Aces-Electronics/ae-p703-screens/Front/FrontIO_Screen_Software/gui_project/ae/cache/thumb_362581445pirate_camp_co_290.png

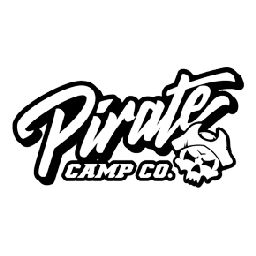
Front/FrontIO_Screen_Software/gui_project/ae/cache/thumb_362581445pirate_camp_co_290.png
