Aces-Electronics/ae-p703-screens/Rear/RearIO_MPPT/lifepo4_settings.webp

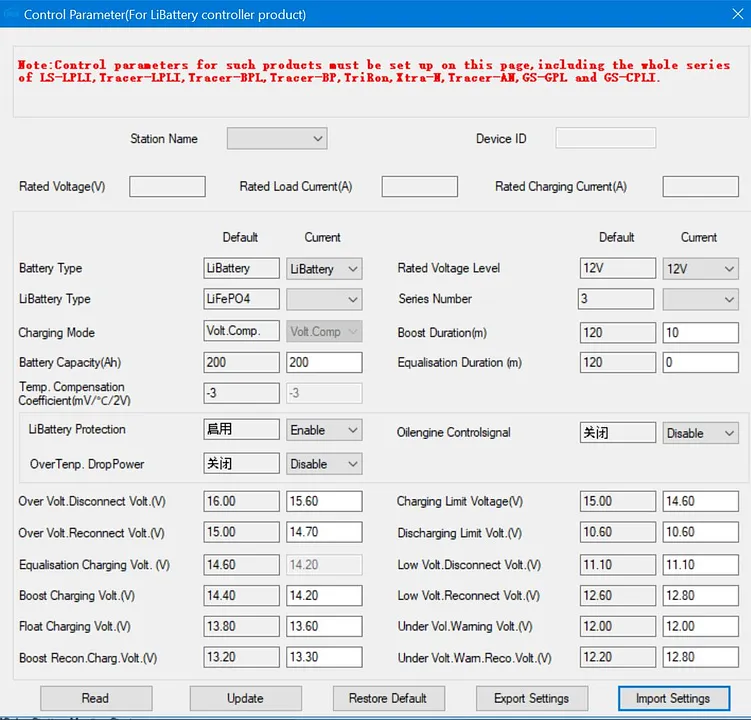
Rear/RearIO_MPPT/lifepo4_settings.webp
