Aces-Electronics/ae-p703-screens/Rear/RearIO_Screen_and_Battery_Cradle/DXF/folding/cradle_rear.dxf.png

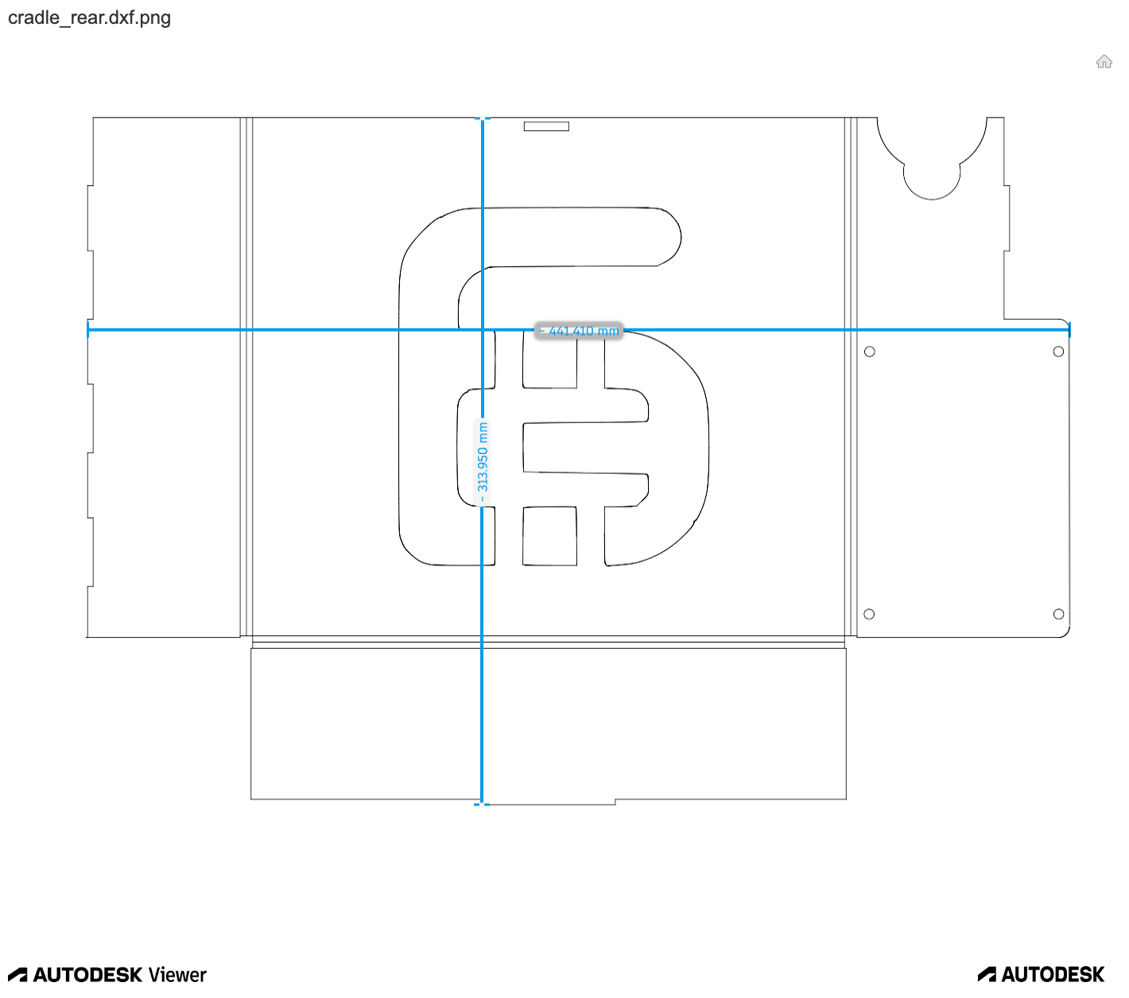
Rear/RearIO_Screen_and_Battery_Cradle/DXF/folding/cradle_rear.dxf.png
