Aces-Electronics/ae-p703-screens/Rear/RearIO_Screen_and_Battery_Cradle/DXF/folding/panel.dxf.png

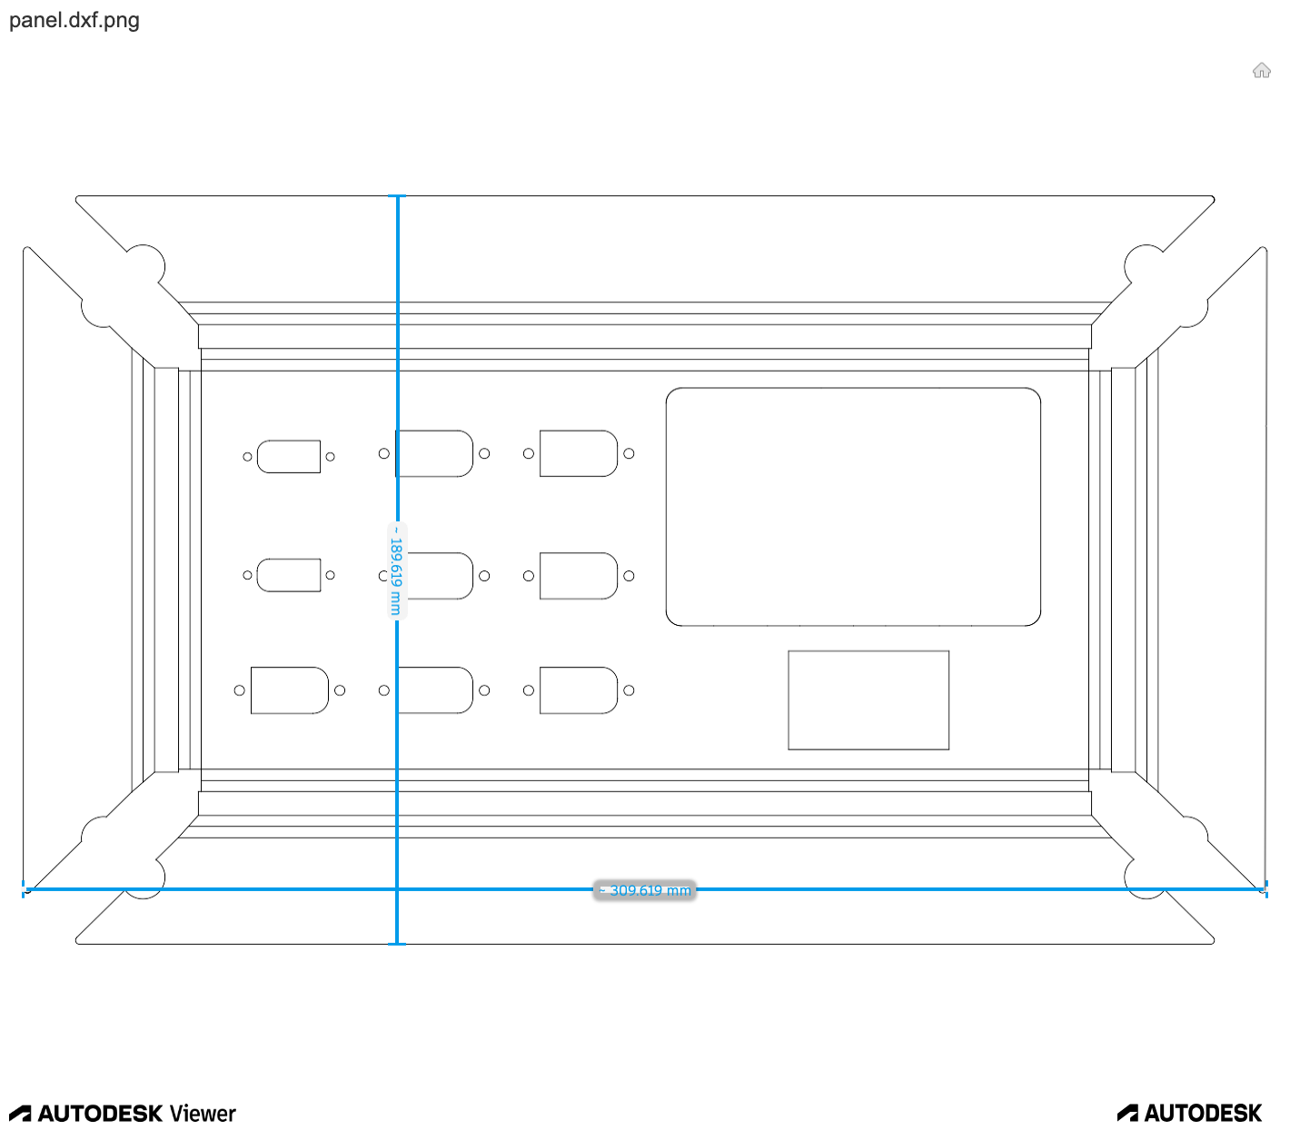
Rear/RearIO_Screen_and_Battery_Cradle/DXF/folding/panel.dxf.png
